sabas1080/agv_bluetooth/AGV/Pruebas y mas/16f819/encoder.h

#include <16F819.h>
#device adc=8

#FUSES NOWDT                 	//No Watch Dog Timer
#FUSES HS                    	//High speed Osc (> 4mhz for PCM/PCH) (>10mhz for PCD)
#FUSES PUT                   	//Power Up Timer
#FUSES MCLR                  	//Master Clear pin enabled
#FUSES NOBROWNOUT            	//No brownout reset
#FUSES NOLVP                 	//No low voltage prgming, B3(PIC16) or B5(PIC18) used for I/O
#FUSES NOCPD                 	//No EE protection
#FUSES NOWRT                 	//Program memory not write protected
#FUSES NODEBUG               	//No Debug mode for ICD
#FUSES NOPROTECT             	//Code not protected from reading

#use delay(clock=4000000)
