sabas1080/agv_bluetooth/AGV/Pruebas y mas/16f819/encoderssp.c

#include <encoderssp.h>




void main()
{

   setup_adc_ports(NO_ANALOGS);
   setup_adc(ADC_CLOCK_DIV_2);
   setup_timer_0(RTCC_INTERNAL|RTCC_DIV_1);
   setup_timer_1(T1_DISABLED);
   setup_timer_2(T2_DISABLED,0,1);
   setup_ccp1(CCP_OFF);

   //TODO: User Code

}
